GiroPetrenko/10g4psw/screenshots/1.jpg

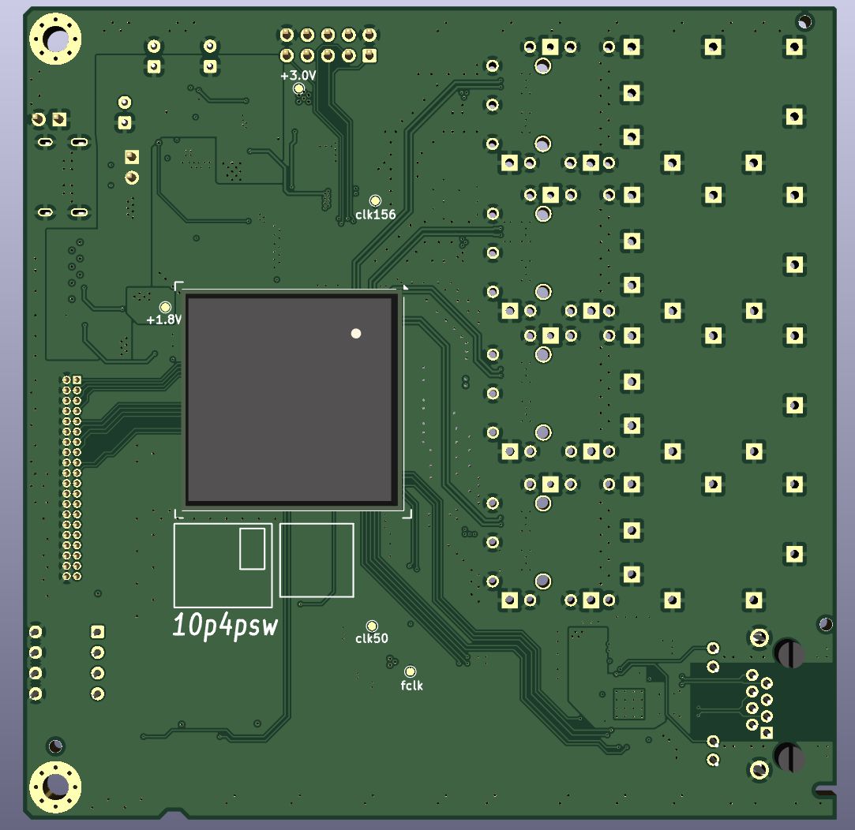
screenshots/1.jpg
