GiroPetrenko/10g4psw/10p_4psw.kicad_sch

## KiCad design 10p_4psw.kicad_sch (2025-11-05)

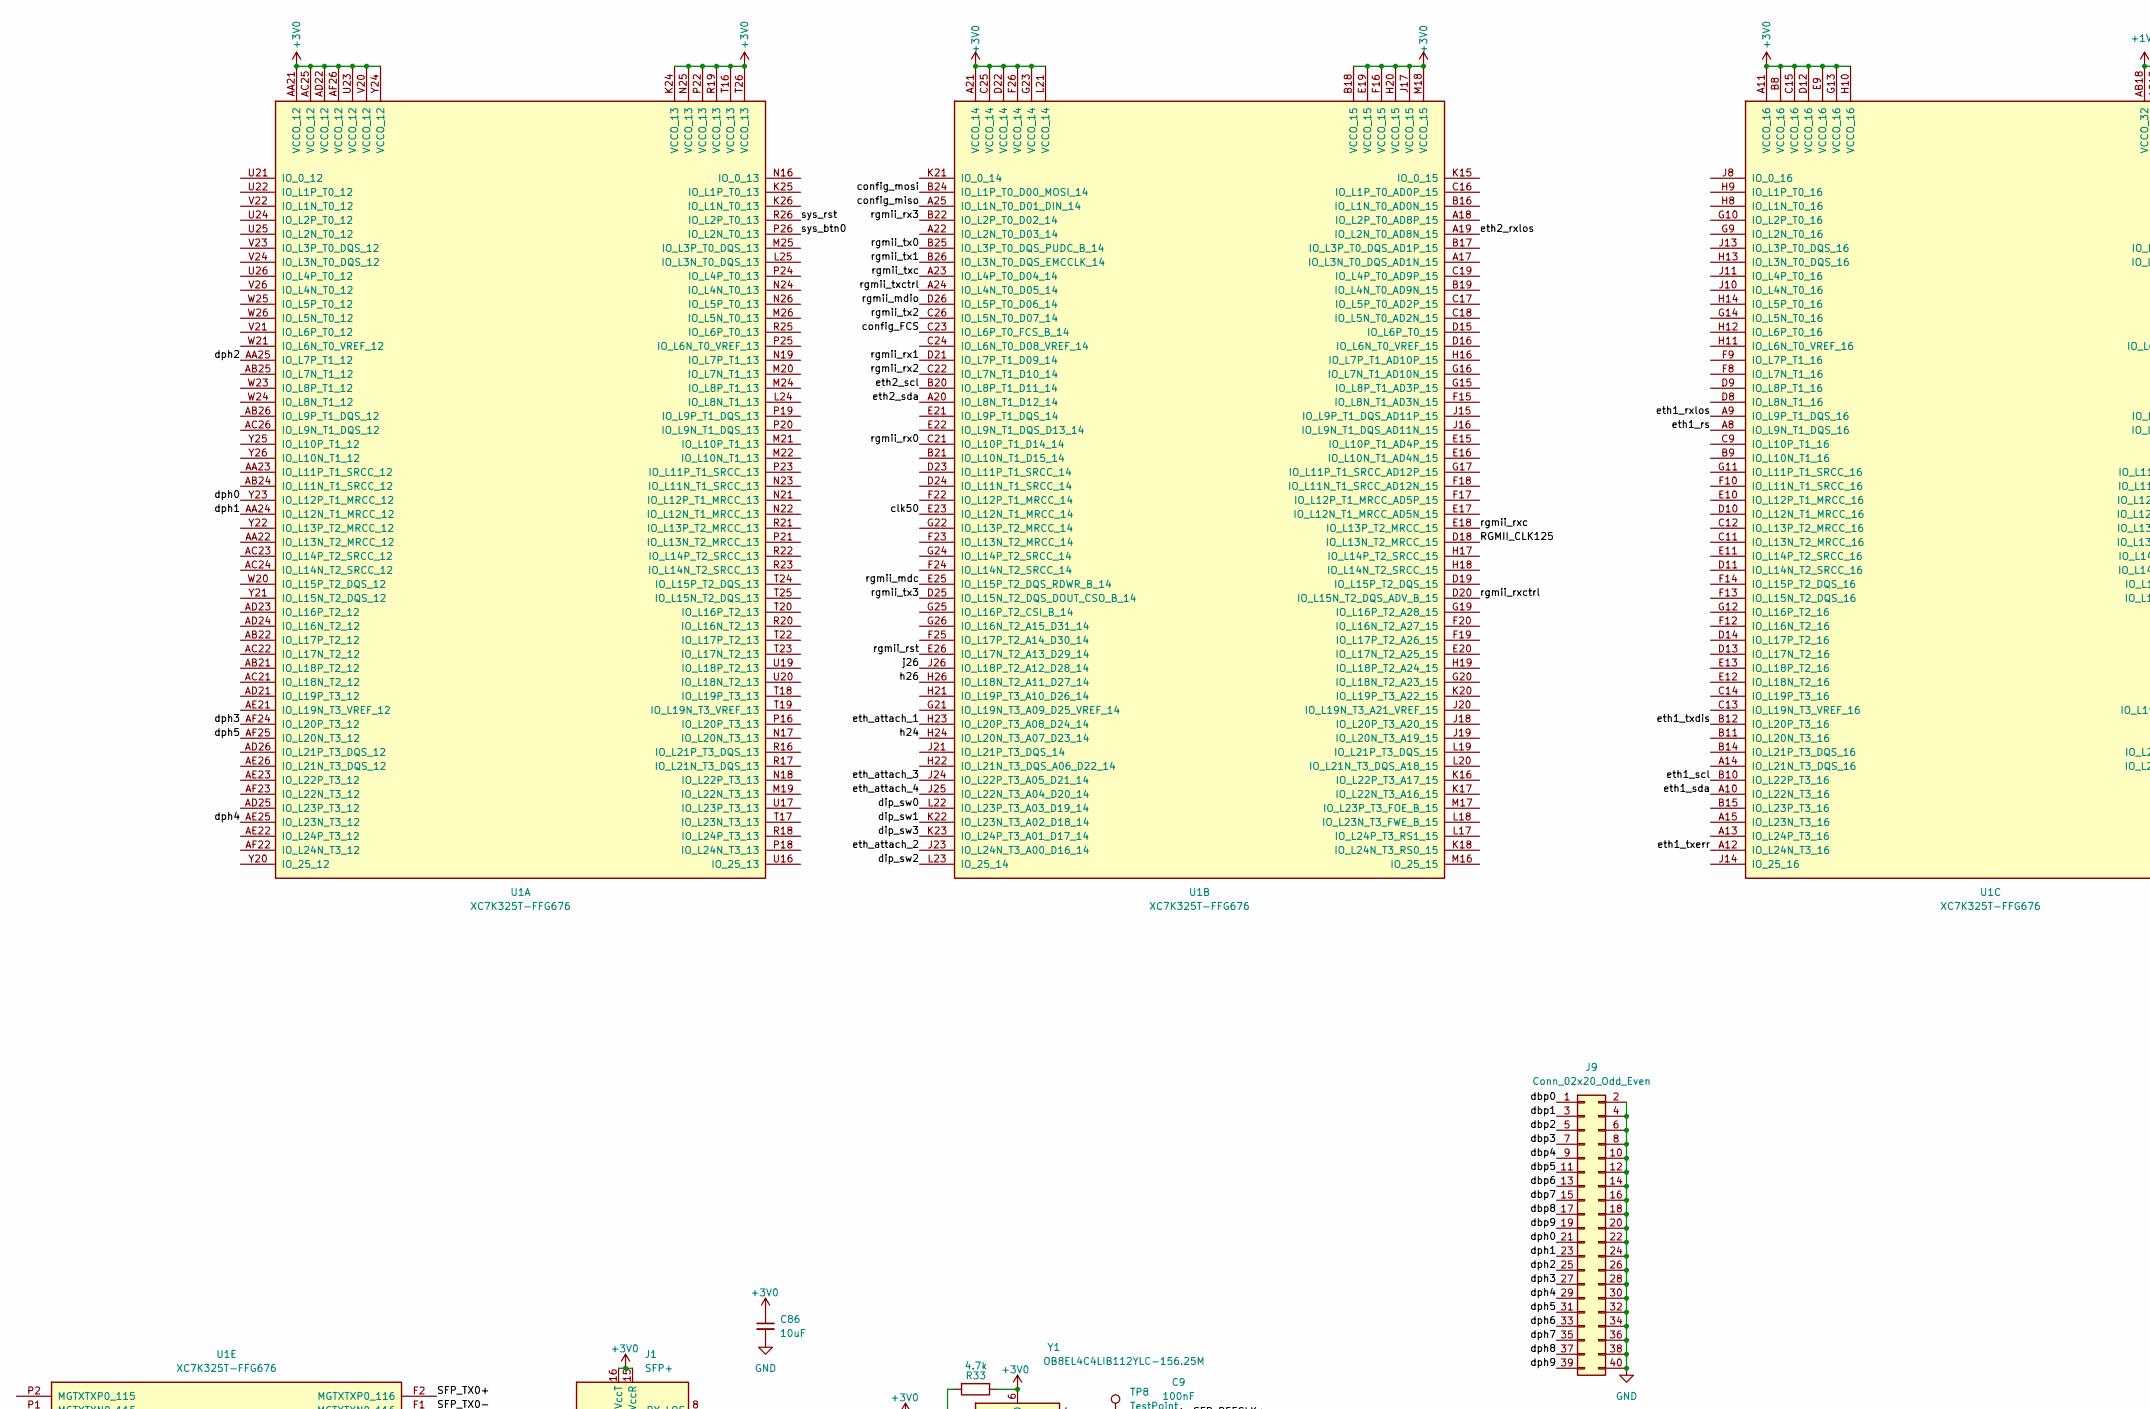
[picture p5: schematic 10p_4psw.kicad_sch, part in row 1, column 1]

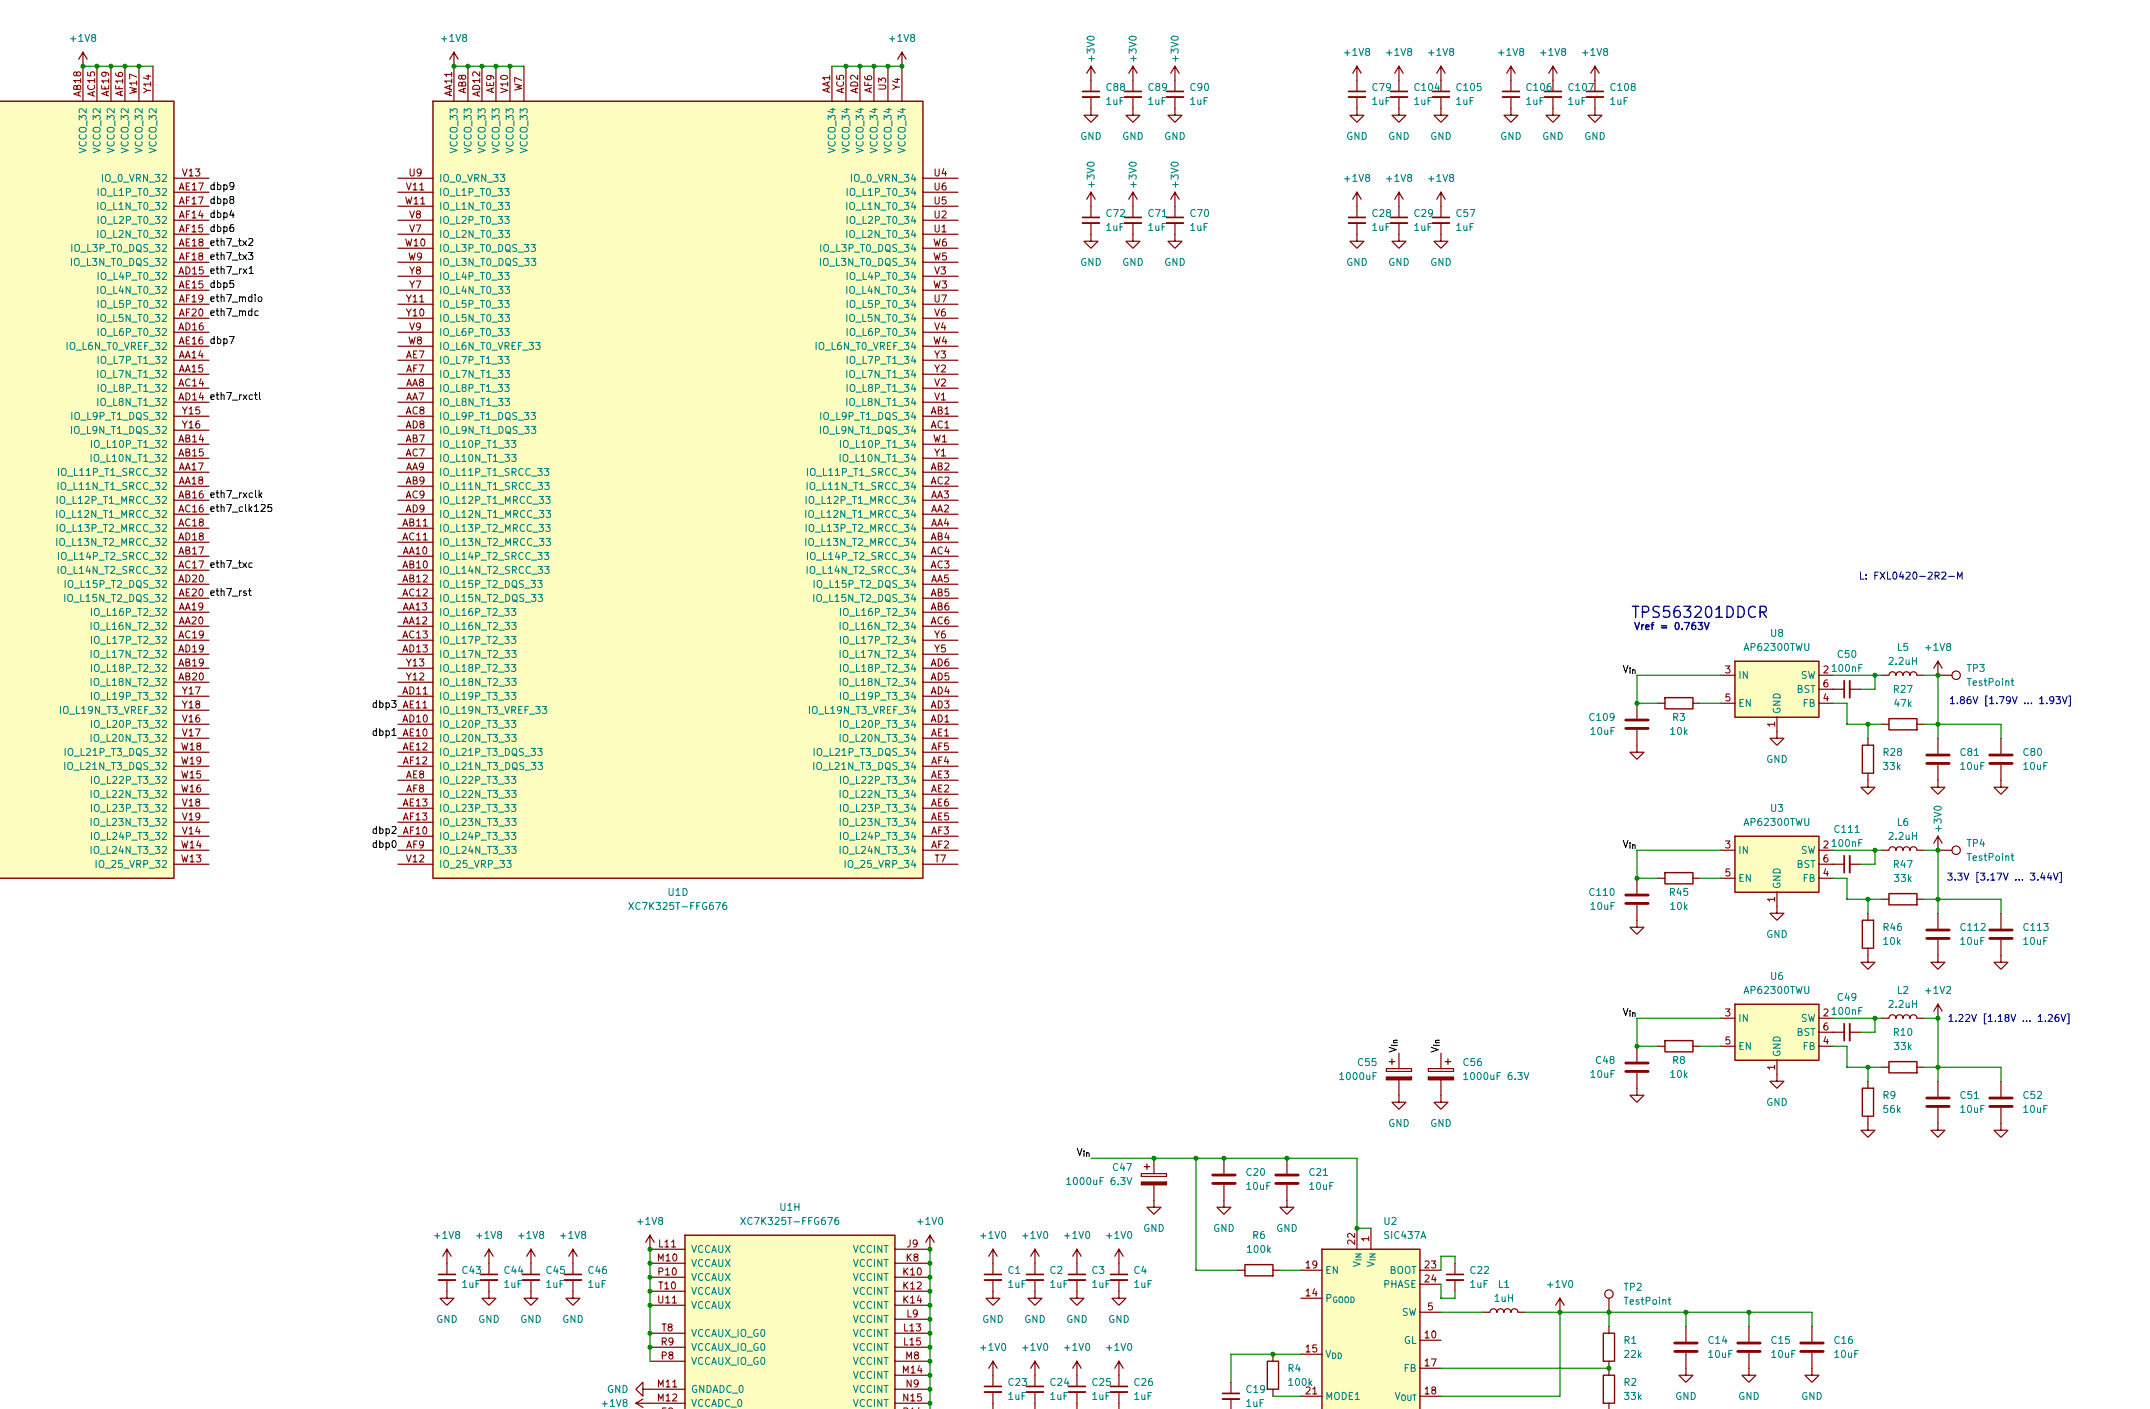
[picture p6: schematic 10p_4psw.kicad_sch, part in row 1, column 2]

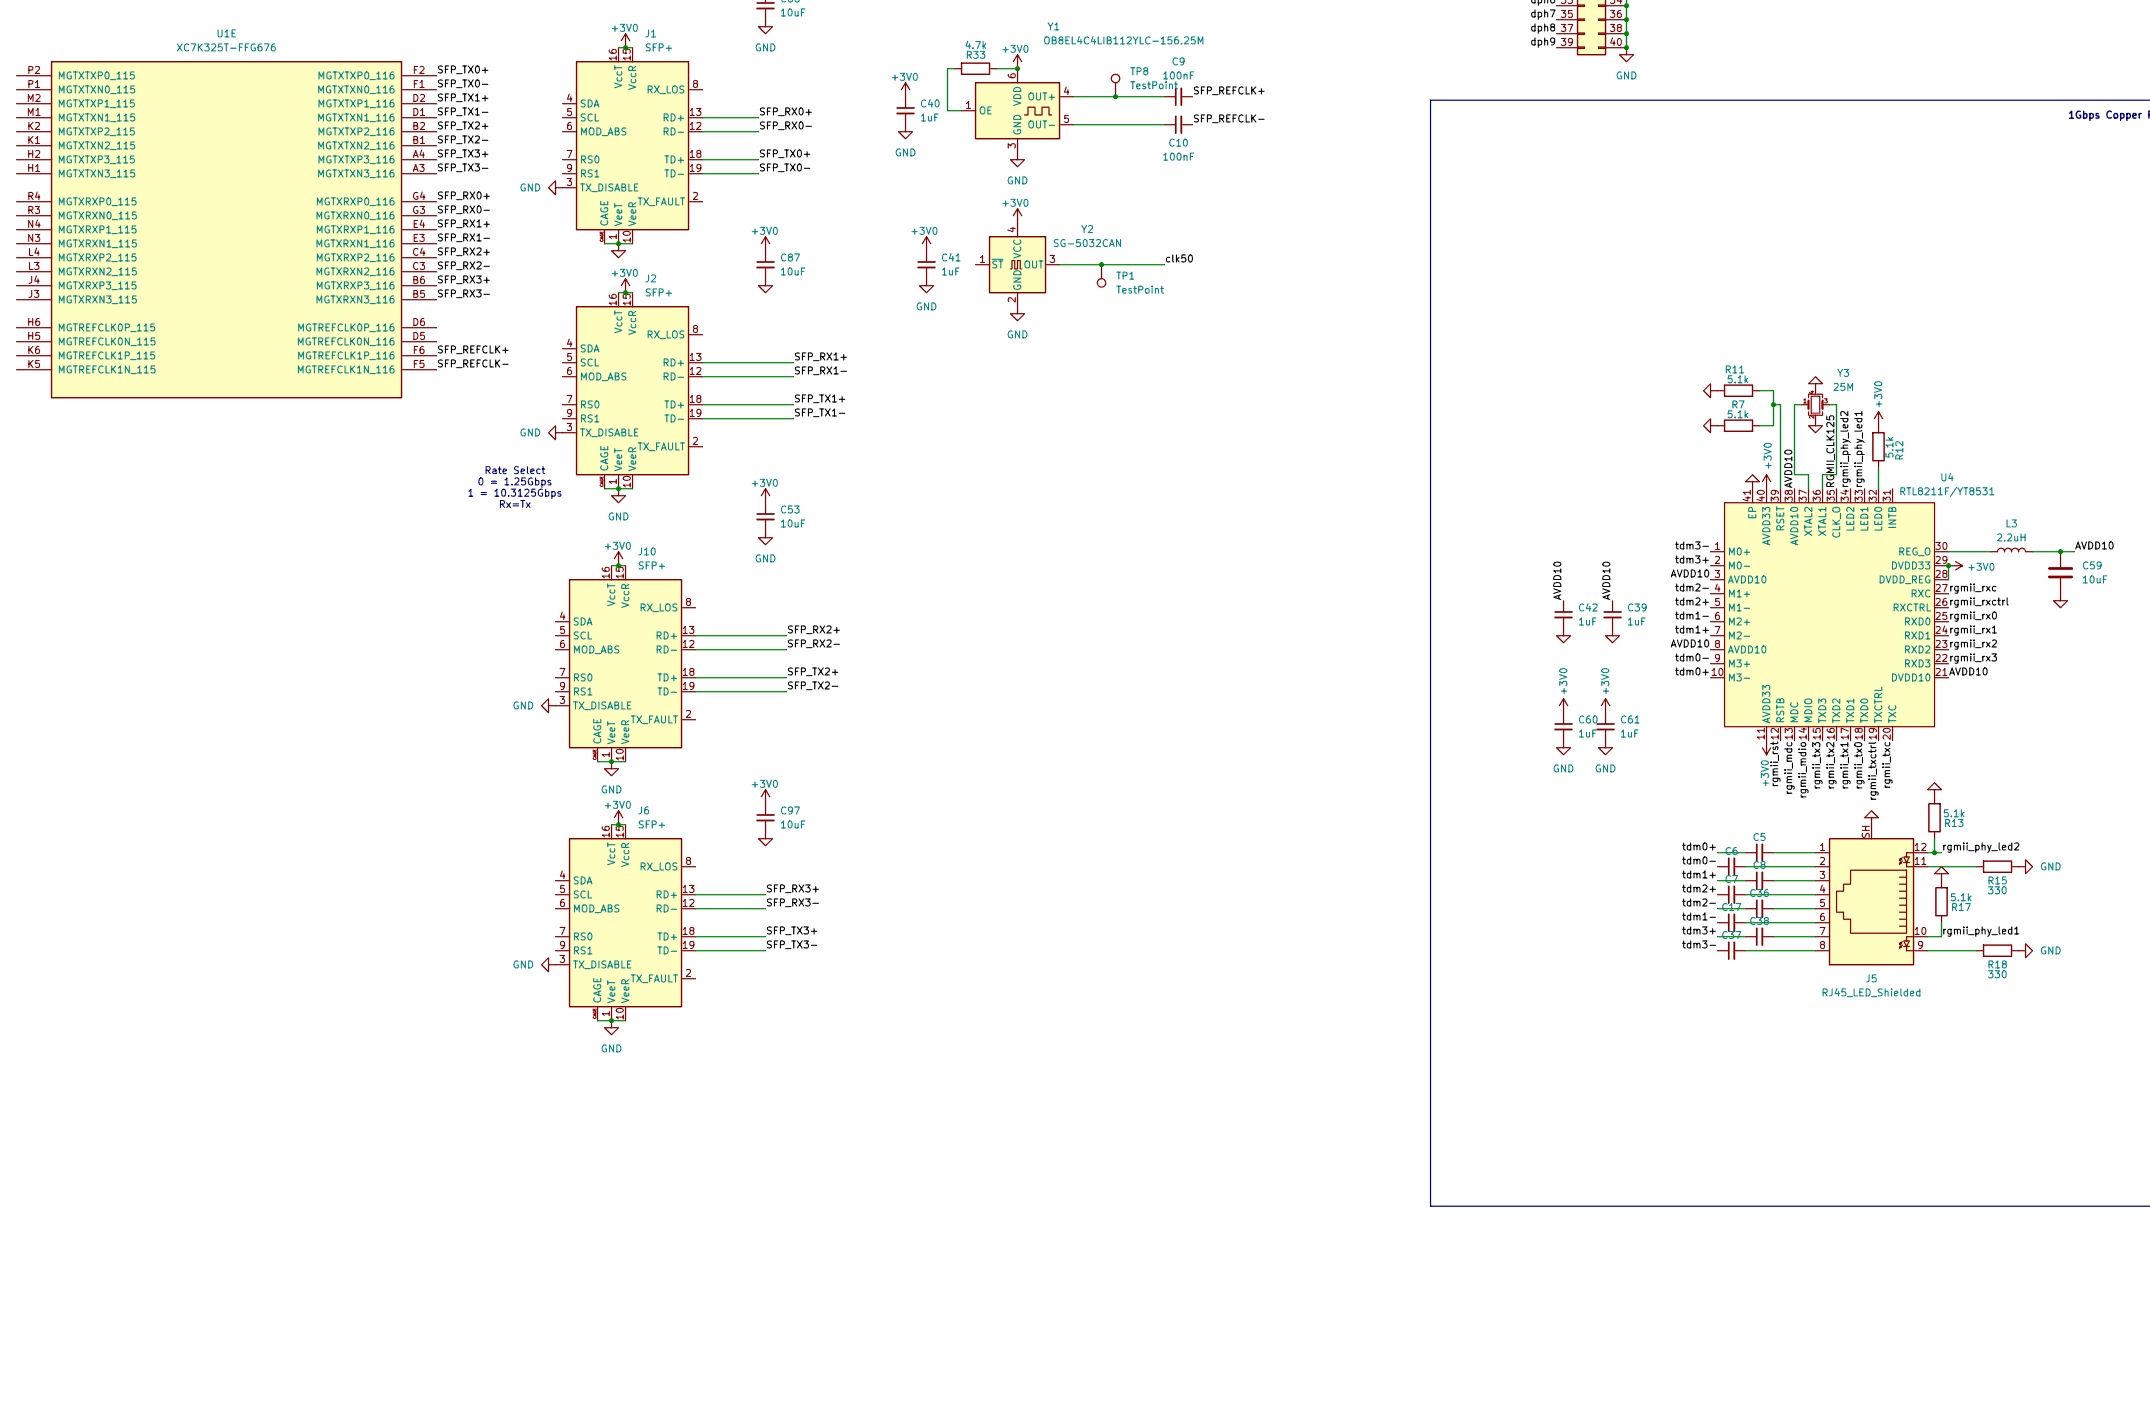
[picture p7: schematic 10p_4psw.kicad_sch, part in row 2, column 1]

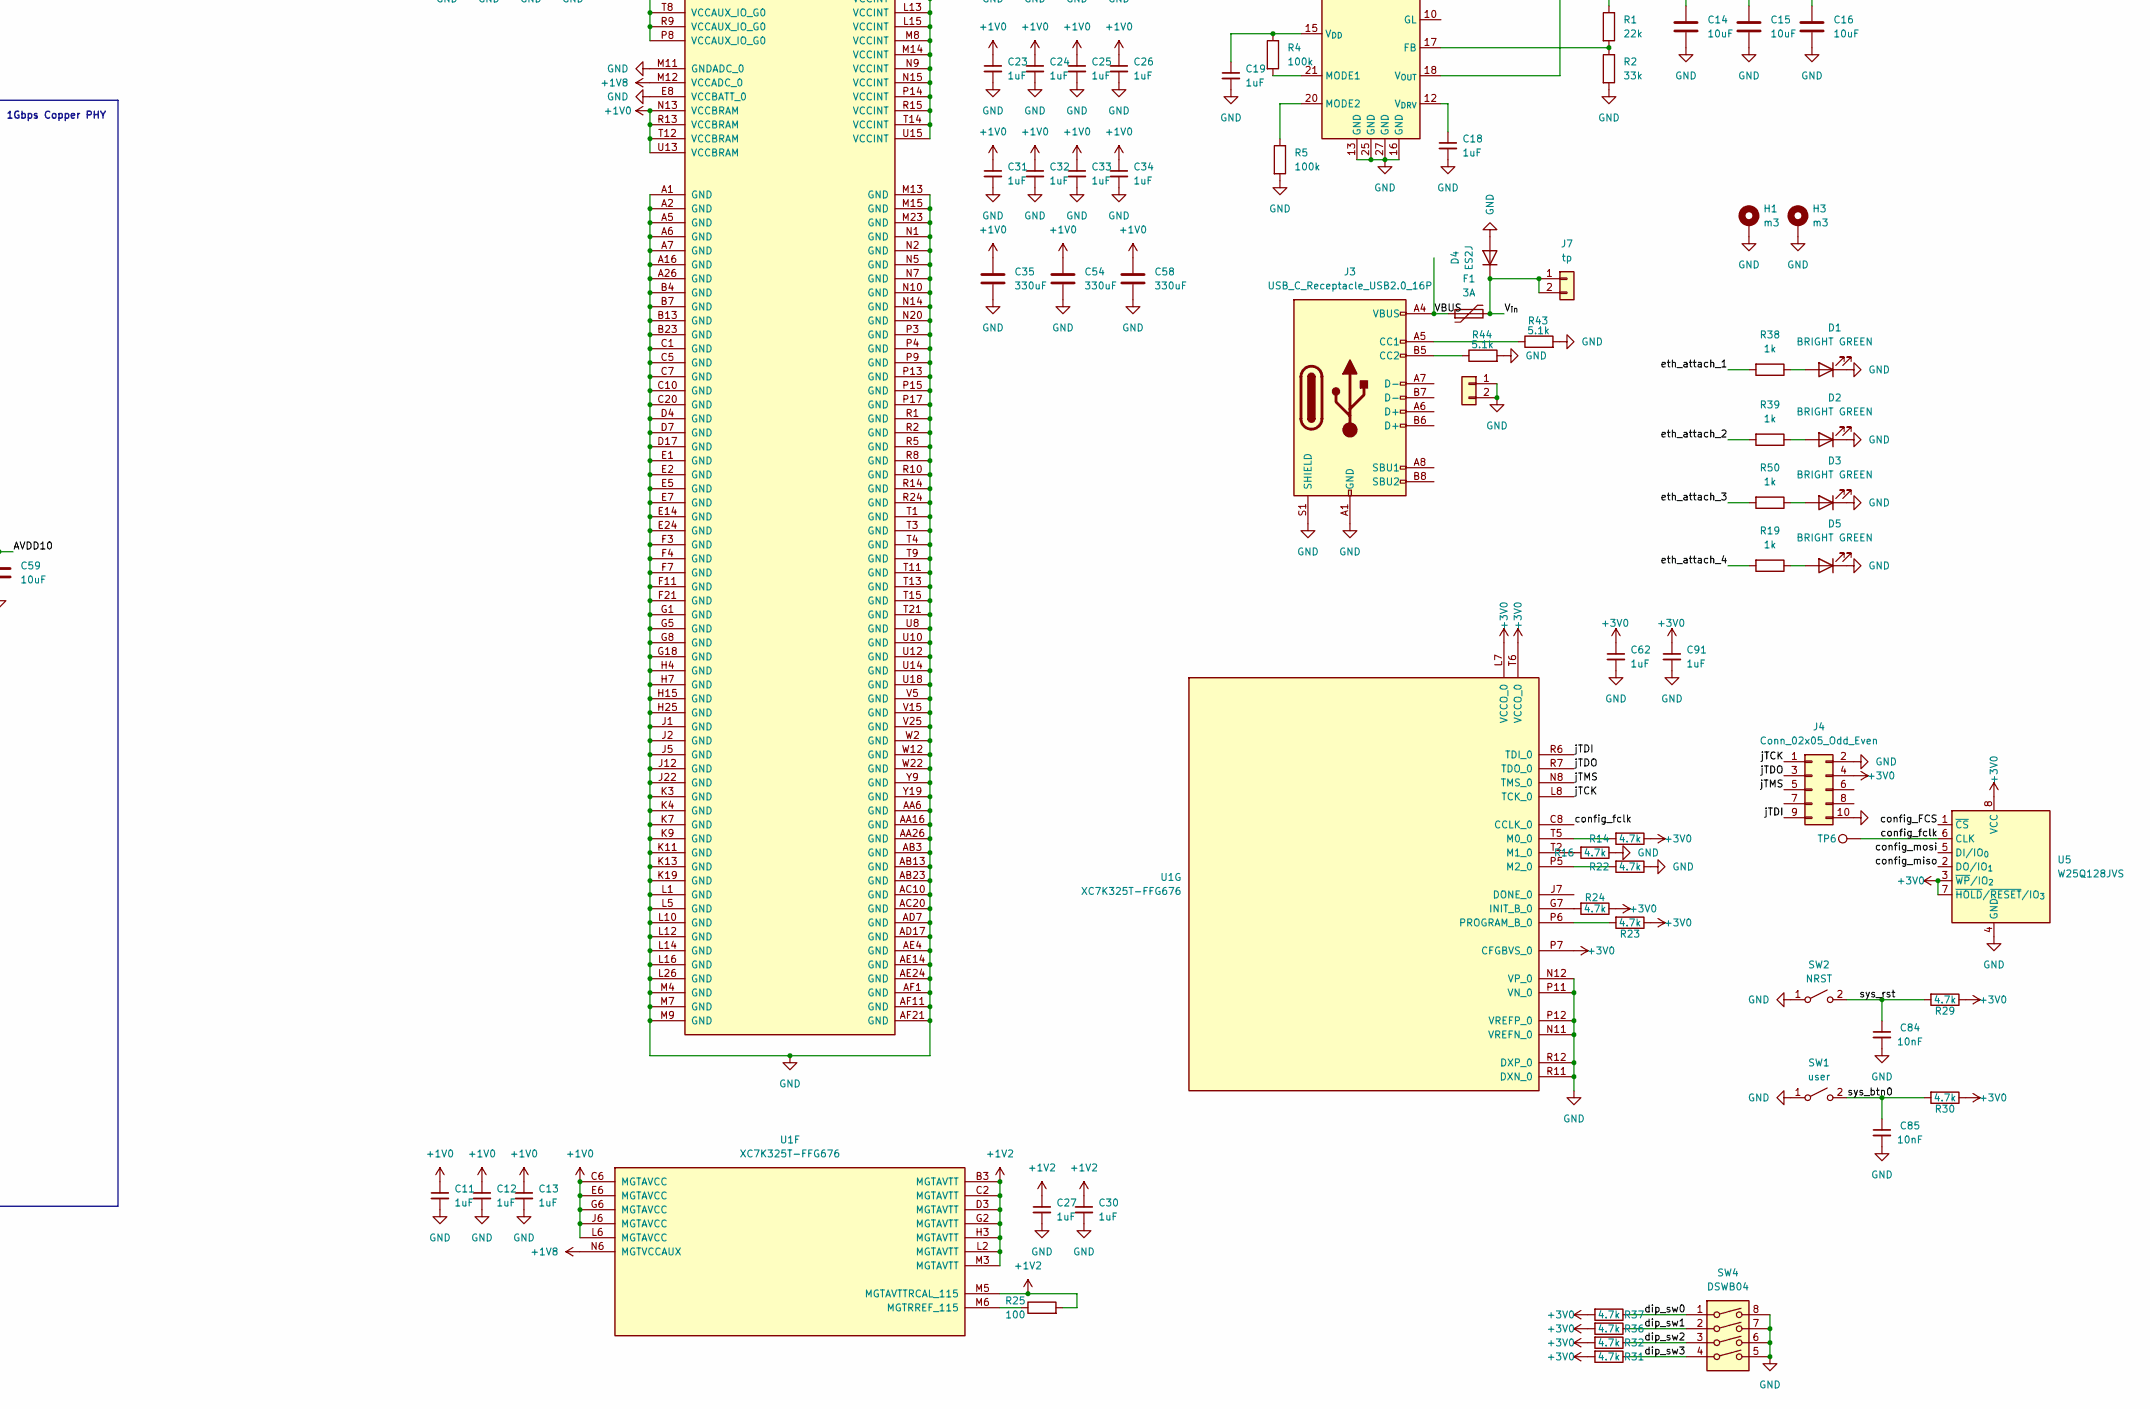
[picture p8: schematic 10p_4psw.kicad_sch, part in row 2, column 2]

Parts:
C1, C2, C3, C4, C5, C6, C7, C8, C11, C12, C13, C17, C18, C19, C22, C23, C24, C25, C26, C27, C28, C29, C30, C31, C32, C33, C34, C36, C37, C38, C39, C40, C41, C42, C43, C44, C45, C46, C57, C60, C61, C62, C70, C71, C72, C79, C88, C89, C90, C91, C104, C105, C106, C107, C108: 1uF; C_0402_1005Metric
C9, C10, C49, C50, C111: 100nF; C_0402_1005Metric
C14, C15, C16, C20, C21, C48, C51, C52, C53, C59, C80, C81, C86, C87, C97, C109, C110, C112, C113: 10uF; C_0805_2012Metric
C35, C54, C58: 330uF; C_1210_3225Metric
C47, C56: 1000uF 6.3V; CP_Radial_D6.3mm_P2.50mm
C55: 1000uF; CP_Radial_D6.3mm_P2.50mm
C84, C85: 10nF; C_0402_1005Metric
D1, D2, D3, D5: BRIGHT GREEN; LED_0805_2012Metric
D4: ES2J; D_SMB
F1: 3A; R_1812_4532Metric
H1, H3: m3; MountingHole_3.2mm_M3_Pad_Via
J1, J2, J6, J10: SFP+; Connector_SFP_and_Cage
J3: USB_C_Receptacle_USB2.0_16P; USB_C_12pin_usb2only_pwr
J4: Conn_02x05_Odd_Even; IDC-Header_2x05_P2.54mm_Vertical
J5: RJ45_LED_Shielded; RJ45_Amphenol_RJHSE538X
J7, J8: tp; PinHeader_1x02_P2.54mm_Vertical
J9: Conn_02x20_Odd_Even; PinHeader_2x20_P1.27mm_Vertical
L1: 1uH; L_1010_largePAD
L2, L3, L5, L6: 2.2uH; L_Sunlord_MWSA0412S
R1: 22k; R_0603_1608Metric
R2, R10, R28, R47: 33k; R_0603_1608Metric
R3, R8, R45: 10k; R_0402_1005Metric
R4, R5, R6: 100k; R_0603_1608Metric
R7, R11, R12, R13, R17, R43, R44: 5.1k; R_0402_1005Metric
R9: 56k; R_0603_1608Metric
R14, R16, R22, R23, R24, R29, R30, R31, R32, R33, R36, R37: 4.7k; R_0402_1005Metric
R15, R18: 330; R_0402_1005Metric
R19, R38, R39, R50: 1k; R_0603_1608Metric
R25: 100; R_0402_1005Metric
R27: 47k; R_0603_1608Metric
R46: 10k; R_0603_1608Metric
SW1: user; PTS645_btn3225_compat
SW2: NRST; PTS645_btn3225_compat
SW4: DSWB04; SW_DIP_SPSTx04_Slide_9.78x12.34mm_W7.62mm_P2.54mm
TP1, TP2, TP3, TP4, TP6, TP8: TestPoint; TestPoint_Pad_D1.0mm
U1: XC7K325T-FFG676; Xilinx_FFG676
U2: SIC437A; SiC43x_PowerPAK_MLP44
U3, U6, U8: AP62300TWU; TSOT-23-6
U4: RTL8211F/YT8531; QFN-40-1EP_5x5mm_P0.4mm_EP3.6x3.6mm_ThermalVias
U5: W25Q128JVS; SOIC-8_5.3x5.3mm_P1.27mm
Y1: OB8EL4C4LIB112YLC-156.25M; Oscillator_SMD_IDT_JS6-6_5.0x3.2mm_P1.27mm
Y2: SG-5032CAN; Oscillator_SMD_EuroQuartz_XO53-4Pin_5.0x3.2mm
Y3: 25M; Crystal_SMD_3225-4Pin_3.2x2.5mm

Connections:
+1V0: C1.1, C2.1, C3.1, C4.1, C11.1, C12.1, C13.1, C14.1, C15.1, C16.1, C23.1, C24.1, C25.1, C26.1, C31.1, C32.1, C33.1, C34.1, C35.1, C54.1, C58.1, L1.2, R1.1, TP2.1, U1.C6 (MGTAVCC), U1.E6 (MGTAVCC), U1.G6 (MGTAVCC), U1.J6 (MGTAVCC), U1.J9 (VCCINT), U1.K8 (VCCINT), U1.K10 (VCCINT), U1.K12 (VCCINT), U1.K14 (VCCINT), U1.L6 (MGTAVCC), U1.L9 (VCCINT), U1.L13 (VCCINT), U1.L15 (VCCINT), U1.M8 (VCCINT), U1.M14 (VCCINT), U1.N9 (VCCINT), U1.N13 (VCCBRAM), U1.N15 (VCCINT), U1.P14 (VCCINT), U1.R13 (VCCBRAM), U1.R15 (VCCINT), U1.T12 (VCCBRAM), U1.T14 (VCCINT), U1.U13 (VCCBRAM), U1.U15 (VCCINT), U2.18 (V_{OUT})
+1V2: C27.1, C30.1, C51.1, C52.1, L2.2, R10.2, R25.2, U1.B3 (MGTAVTT), U1.C2 (MGTAVTT), U1.D3 (MGTAVTT), U1.G2 (MGTAVTT), U1.H3 (MGTAVTT), U1.L2 (MGTAVTT), U1.M3 (MGTAVTT), U1.M5 (MGTAVTTRCAL_115)
+1V8: C28.1, C29.1, C43.1, C44.1, C45.1, C46.1, C57.1, C79.1, C80.1, C81.1, C104.1, C105.1, C106.1, C107.1, C108.1, L5.2, R27.2, TP3.1, U1.AA1 (VCCO_34), U1.AA11 (VCCO_33), U1.AB8 (VCCO_33), U1.AB18 (VCCO_32), U1.AC5 (VCCO_34), U1.AC15 (VCCO_32), U1.AD2 (VCCO_34), U1.AD12 (VCCO_33), U1.AE9 (VCCO_33), U1.AE19 (VCCO_32), U1.AF6 (VCCO_34), U1.AF16 (VCCO_32), U1.L11 (VCCAUX), U1.M10 (VCCAUX), U1.M12 (VCCADC_0), U1.N6 (MGTVCCAUX), U1.P8 (VCCAUX_IO_G0), U1.P10 (VCCAUX), U1.R9 (VCCAUX_IO_G0), U1.T8 (VCCAUX_IO_G0), U1.T10 (VCCAUX), U1.U3 (VCCO_34), U1.U11 (VCCAUX), U1.V10 (VCCO_33), U1.W7 (VCCO_33), U1.W17 (VCCO_32), U1.Y4 (VCCO_34), U1.Y14 (VCCO_32)
+3V0: C40.1, C41.1, C53.1, C60.1, C61.1, C62.1, C70.1, C71.1, C72.1, C86.1, C87.1, C88.1, C89.1, C90.1, C91.1, C97.1, C112.1, C113.1, J1.15 (VccR), J1.16 (VccT), J2.15 (VccR), J2.16 (VccT), J4.4, J6.15 (VccR), J6.16 (VccT), J10.15 (VccR), J10.16 (VccT), L6.2, R12.2, R14.1, R23.1, R24.1, R29.1, R30.1, R31.2, R32.2, R33.1, R36.2, R37.2, R47.2, TP4.1, U1.A11 (VCCO_16), U1.A21 (VCCO_14), U1.AA21 (VCCO_12), U1.AC25 (VCCO_12), U1.AD22 (VCCO_12), U1.AF26 (VCCO_12), U1.B8 (VCCO_16), U1.B18 (VCCO_15), U1.C15 (VCCO_16), U1.C25 (VCCO_14), U1.D12 (VCCO_16), U1.D22 (VCCO_14), U1.E9 (VCCO_16), U1.E19 (VCCO_15), U1.F16 (VCCO_15), U1.F26 (VCCO_14), U1.G13 (VCCO_16), U1.G23 (VCCO_14), U1.H10 (VCCO_16), U1.H20 (VCCO_15), U1.J17 (VCCO_15), U1.K24 (VCCO_13), U1.L7 (VCCO_0), U1.L21 (VCCO_14), U1.M18 (VCCO_15), U1.N25 (VCCO_13), U1.P7 (CFGBVS_0), U1.P22 (VCCO_13), U1.R19 (VCCO_13), U1.T6 (VCCO_0), U1.T16 (VCCO_13), U1.T26 (VCCO_13), U1.U23 (VCCO_12), U1.V20 (VCCO_12), U1.Y24 (VCCO_12), U4.11 (AVDD33), U4.28 (DVDD_REG), U4.29 (DVDD33), U4.40 (AVDD33), U5.3 (~WP/IO_{2}), U5.7 (~HOLD/~RESET/IO_{3}), U5.8 (VCC), Y1.6 (VDD), Y2.4 (VCC)
AVDD10: C39.1, C42.1, C59.1, L3.2, U4.3 (AVDD10), U4.8 (AVDD10), U4.21 (DVDD10), U4.38 (AVDD10)
GND: C1.2, C2.2, C3.2, C4.2, C11.2, C12.2, C13.2, C14.2, C15.2, C16.2, C18.2, C19.2, C20.2, C21.2, C23.2, C24.2, C25.2, C26.2, C27.2, C28.2, C29.2, C30.2, C31.2, C32.2, C33.2, C34.2, C35.2, C39.2, C40.2, C41.2, C42.2, C43.2, C44.2, C45.2, C46.2, C47.2, C48.2, C51.2, C52.2, C53.2, C54.2, C55.2, C56.2, C57.2, C58.2, C59.2, C60.2, C61.2, C62.2, C70.2, C71.2, C72.2, C79.2, C80.2, C81.2, C84.2, C85.2, C86.2, C87.2, C88.2, C89.2, C90.2, C91.2, C97.2, C104.2, C105.2, C106.2, C107.2, C108.2, C109.2, C110.2, C112.2, C113.2, D1.1 (K), D2.1 (K), D3.1 (K), D4.2 (A), D5.1 (K), H1.1, H3.1, J1.1 (VeeT), J1.3 (TX_DISABLE), J1.10 (VeeR), J1.11 (VeeR), J1.14 (VeeR), J1.17 (VeeT), J1.20 (VeeT), J1.CAGE, J2.1 (VeeT), J2.3 (TX_DISABLE), J2.10 (VeeR), J2.11 (VeeR), J2.14 (VeeR), J2.17 (VeeT), J2.20 (VeeT), J2.CAGE, J3.A1 (GND), J3.A12 (GND), J3.B1 (GND), J3.B12 (GND), J3.S1 (SHIELD), J4.2, J4.10, J5.SH, J6.1 (VeeT), J6.3 (TX_DISABLE), J6.10 (VeeR), J6.11 (VeeR), J6.14 (VeeR), J6.17 (VeeT), J6.20 (VeeT), J6.CAGE, J8.1, J8.2, J9.2, J9.4, J9.6, J9.8, J9.10, J9.12, J9.14, J9.16, J9.18, J9.20, J9.22, J9.24, J9.26, J9.28, J9.30, J9.32, J9.34, J9.36, J9.38, J9.40, J10.1 (VeeT), J10.3 (TX_DISABLE), J10.10 (VeeR), J10.11 (VeeR), J10.14 (VeeR), J10.17 (VeeT), J10.20 (VeeT), J10.CAGE, R2.2, R5.2, R7.1, R9.1, R11.1, R13.2, R15.1, R16.1, R17.2, R18.1, R22.1, R28.1, R43.2, R44.2, R46.1, SW1.1 (A), SW2.1 (A), SW4.5, SW4.6, SW4.7, SW4.8, U1.A1 (GND), U1.A2 (GND), U1.A5 (GND), U1.A6 (GND), U1.A7 (GND), U1.A16 (GND), U1.A26 (GND), U1.AA6 (GND), U1.AA16 (GND), U1.AA26 (GND), U1.AB3 (GND), U1.AB13 (GND), U1.AB23 (GND), U1.AC10 (GND), U1.AC20 (GND), U1.AD7 (GND), U1.AD17 (GND), U1.AE4 (GND), U1.AE14 (GND), U1.AE24 (GND), U1.AF1 (GND), U1.AF11 (GND), U1.AF21 (GND), U1.B4 (GND), U1.B7 (GND), U1.B13 (GND), U1.B23 (GND), U1.C1 (GND), U1.C5 (GND), U1.C7 (GND), U1.C10 (GND), U1.C20 (GND), U1.D4 (GND), U1.D7 (GND), U1.D17 (GND), U1.E1 (GND), U1.E2 (GND), U1.E5 (GND), U1.E7 (GND), U1.E8 (VCCBATT_0), U1.E14 (GND), U1.E24 (GND), U1.F3 (GND), U1.F4 (GND), U1.F7 (GND), U1.F11 (GND), U1.F21 (GND), U1.G1 (GND), U1.G5 (GND), U1.G8 (GND), U1.G18 (GND), U1.H4 (GND), U1.H7 (GND), U1.H15 (GND), U1.H25 (GND), U1.J1 (GND), U1.J2 (GND), U1.J5 (GND), U1.J12 (GND), U1.J22 (GND), U1.K3 (GND), U1.K4 (GND), U1.K7 (GND), U1.K9 (GND), U1.K11 (GND), U1.K13 (GND), U1.K19 (GND), U1.L1 (GND), U1.L5 (GND), U1.L10 (GND), U1.L12 (GND), U1.L14 (GND), U1.L16 (GND), U1.L26 (GND), U1.M4 (GND), U1.M7 (GND), U1.M9 (GND), U1.M11 (GNDADC_0), U1.M13 (GND), U1.M15 (GND), U1.M23 (GND), U1.N1 (GND), U1.N2 (GND), U1.N5 (GND), U1.N7 (GND), U1.N10 (GND), U1.N11 (VREFN_0), U1.N12 (VP_0), U1.N14 (GND), U1.N20 (GND), U1.P3 (GND), U1.P4 (GND), U1.P9 (GND), U1.P11 (VN_0), U1.P12 (VREFP_0), U1.P13 (GND), U1.P15 (GND), U1.P17 (GND), U1.R1 (GND), U1.R2 (GND), U1.R5 (GND), U1.R8 (GND), U1.R10 (GND), U1.R11 (DXN_0), U1.R12 (DXP_0), U1.R14 (GND), U1.R24 (GND), U1.T1 (GND), U1.T3 (GND), U1.T4 (GND), U1.T9 (GND), U1.T11 (GND), U1.T13 (GND), U1.T15 (GND), U1.T21 (GND), U1.U8 (GND), U1.U10 (GND), U1.U12 (GND), U1.U14 (GND), U1.U18 (GND), U1.V5 (GND), U1.V15 (GND), U1.V25 (GND), U1.W2 (GND), U1.W12 (GND), U1.W22 (GND), U1.Y9 (GND), U1.Y19 (GND), U2.13 (GND), U2.16 (GND), U2.25 (GND), U2.27 (GND), U3.1 (GND), U4.41 (EP), U5.4 (GND), U6.1 (GND), U8.1 (GND), Y1.3 (GND), Y2.2 (GND), Y3.2, Y3.4
unnamed: C5.2, J5.1
unnamed: C6.2, J5.2
unnamed: C7.2, J5.4
unnamed: C8.2, J5.3
unnamed: C9.1, TP8.1, Y1.4 (OUT+)
unnamed: C10.1, Y1.5 (OUT-)
unnamed: C17.2, J5.6
unnamed: C18.1, U2.12 (V_{DRV})
unnamed: C19.1, R4.1, U2.15 (V_{DD})
unnamed: C22.1, U2.23 (BOOT)
unnamed: C22.2, U2.24 (PHASE)
unnamed: C36.2, J5.5
unnamed: C37.2, J5.8
unnamed: C38.2, J5.7
unnamed: C49.1, U6.6 (BST)
unnamed: C49.2, L2.1, U6.2 (SW)
unnamed: C50.1, U8.6 (BST)
unnamed: C50.2, L5.1, U8.2 (SW)
unnamed: C111.1, U3.6 (BST)
unnamed: C111.2, L6.1, U3.2 (SW)
unnamed: D1.2 (A), R38.1
unnamed: D2.2 (A), R39.1
unnamed: D3.2 (A), R50.1
unnamed: D5.2 (A), R19.1
unnamed: J3.A5 (CC1), R43.1
unnamed: J3.B5 (CC2), R44.1
unnamed: J5.9, R18.2
unnamed: J5.11, R15.2
unnamed: L1.1, U2.5 (SW)
unnamed: L3.1, U4.30 (REG_O)
unnamed: R1.2, R2.1, U2.17 (FB)
unnamed: R3.1, U8.5 (EN)
unnamed: R4.2, U2.21 (MODE1)
unnamed: R5.1, U2.20 (MODE2)
unnamed: R6.2, U2.19 (EN)
unnamed: R8.1, U6.5 (EN)
unnamed: R9.2, R10.1, U6.4 (FB)
unnamed: R7.2, R11.2, U4.39 (RSET)
unnamed: R12.1, U4.32 (LED0)
unnamed: R14.2, U1.T5 (M0_0)
unnamed: R16.2, U1.T2 (M1_0)
unnamed: R22.2, U1.P5 (M2_0)
unnamed: R23.2, U1.P6 (PROGRAM_B_0)
unnamed: R24.2, U1.G7 (INIT_B_0)
unnamed: R25.1, U1.M6 (MGTRREF_115)
unnamed: R27.1, R28.2, U8.4 (FB)
unnamed: R33.2, Y1.1 (OE)
unnamed: R45.1, U3.5 (EN)
unnamed: R46.2, R47.1, U3.4 (FB)
unnamed: U2.10 (GL), U2.11 (GL), U2.28 (GL)
unnamed: U4.36 (XTAL1), Y3.3
unnamed: U4.37 (XTAL2), Y3.1
RGMII_CLK125: U1.D18 (IO_L13N_T2_MRCC_15), U4.35 (CLK_O)
SFP_REFCLK+: C9.2, U1.F6 (MGTREFCLK1P_116)
SFP_REFCLK-: C10.2, U1.F5 (MGTREFCLK1N_116)
SFP_RX0+: J1.13 (RD+), U1.G4 (MGTXRXP0_116)
SFP_RX0-: J1.12 (RD-), U1.G3 (MGTXRXN0_116)
SFP_RX1+: J2.13 (RD+), U1.E4 (MGTXRXP1_116)
SFP_RX1-: J2.12 (RD-), U1.E3 (MGTXRXN1_116)
SFP_RX2+: J10.13 (RD+), U1.C4 (MGTXRXP2_116)
SFP_RX2-: J10.12 (RD-), U1.C3 (MGTXRXN2_116)
SFP_RX3+: J6.13 (RD+), U1.B6 (MGTXRXP3_116)
SFP_RX3-: J6.12 (RD-), U1.B5 (MGTXRXN3_116)
SFP_TX0+: J1.18 (TD+), U1.F2 (MGTXTXP0_116)
SFP_TX0-: J1.19 (TD-), U1.F1 (MGTXTXN0_116)
SFP_TX1+: J2.18 (TD+), U1.D2 (MGTXTXP1_116)
SFP_TX1-: J2.19 (TD-), U1.D1 (MGTXTXN1_116)
SFP_TX2+: J10.18 (TD+), U1.B2 (MGTXTXP2_116)
SFP_TX2-: J10.19 (TD-), U1.B1 (MGTXTXN2_116)
SFP_TX3+: J6.18 (TD+), U1.A4 (MGTXTXP3_116)
SFP_TX3-: J6.19 (TD-), U1.A3 (MGTXTXN3_116)
VBUS: F1.1, J3.A4 (VBUS), J3.A9 (VBUS), J3.B4 (VBUS), J3.B9 (VBUS)
V_{in}: C20.1, C21.1, C47.1, C48.1, C55.1, C56.1, C109.1, C110.1, D4.1 (K), F1.2, J7.1, J7.2, R3.2, R6.1, R8.2, R45.2, U2.1 (V_{IN}), U2.22 (V_{IN}), U3.3 (IN), U6.3 (IN), U8.3 (IN)
clk50: TP1.1, U1.E23 (IO_L12N_T1_MRCC_14), Y2.3 (OUT)
config_FCS: U1.C23 (IO_L6P_T0_FCS_B_14), U5.1 (~CS)
config_fclk: TP6.1, U1.C8 (CCLK_0), U5.6 (CLK)
config_miso: U1.A25 (IO_L1N_T0_D01_DIN_14), U5.2 (DO/IO_{1})
config_mosi: U1.B24 (IO_L1P_T0_D00_MOSI_14), U5.5 (DI/IO_{0})
dbp0: J9.1, U1.AF9 (IO_L24N_T3_33)
dbp1: J9.3, U1.AE10 (IO_L20N_T3_33)
dbp2: J9.5, U1.AF10 (IO_L24P_T3_33)
dbp3: J9.7, U1.AE11 (IO_L19N_T3_VREF_33)
dbp4: J9.9, U1.AF14 (IO_L2P_T0_32)
dbp5: J9.11, U1.AE15 (IO_L4N_T0_32)
dbp6: J9.13, U1.AF15 (IO_L2N_T0_32)
dbp7: J9.15, U1.AE16 (IO_L6N_T0_VREF_32)
dbp8: J9.17, U1.AF17 (IO_L1N_T0_32)
dbp9: J9.19, U1.AE17 (IO_L1P_T0_32)
dip_sw0: R37.1, SW4.1, U1.L22 (IO_L23P_T3_A03_D19_14)
dip_sw1: R36.1, SW4.2, U1.K22 (IO_L23N_T3_A02_D18_14)
dip_sw2: R32.1, SW4.3, U1.L23 (IO_25_14)
dip_sw3: R31.1, SW4.4, U1.K23 (IO_L24P_T3_A01_D17_14)
dph0: J9.21, U1.Y23 (IO_L12P_T1_MRCC_12)
dph1: J9.23, U1.AA24 (IO_L12N_T1_MRCC_12)
dph2: J9.25, U1.AA25 (IO_L7P_T1_12)
dph3: J9.27, U1.AF24 (IO_L20P_T3_12)
dph4: J9.29, U1.AE25 (IO_L23N_T3_12)
dph5: J9.31, U1.AF25 (IO_L20N_T3_12)
dph6: J9.33
dph7: J9.35
dph8: J9.37
dph9: J9.39
eth1_rs: U1.A8 (IO_L9N_T1_DQS_16)
eth1_rxlos: U1.A9 (IO_L9P_T1_DQS_16)
eth1_scl: U1.B10 (IO_L22P_T3_16)
eth1_sda: U1.A10 (IO_L22N_T3_16)
eth1_txdis: U1.B12 (IO_L20P_T3_16)
eth1_txerr: U1.A12 (IO_L24N_T3_16)
eth2_rxlos: U1.A19 (IO_L2N_T0_AD8N_15)
eth2_scl: U1.B20 (IO_L8P_T1_D11_14)
eth2_sda: U1.A20 (IO_L8N_T1_D12_14)
eth7_clk125: U1.AC16 (IO_L12N_T1_MRCC_32)
eth7_mdc: U1.AF20 (IO_L5N_T0_32)
eth7_mdio: U1.AF19 (IO_L5P_T0_32)
eth7_rst: U1.AE20 (IO_L15N_T2_DQS_32)
eth7_rx1: U1.AD15 (IO_L4P_T0_32)
eth7_rxclk: U1.AB16 (IO_L12P_T1_MRCC_32)
eth7_rxctl: U1.AD14 (IO_L8N_T1_32)
eth7_tx2: U1.AE18 (IO_L3P_T0_DQS_32)
eth7_tx3: U1.AF18 (IO_L3N_T0_DQS_32)
eth7_txc: U1.AC17 (IO_L14N_T2_SRCC_32)
eth_attach_1: R38.2, U1.H23 (IO_L20P_T3_A08_D24_14)
eth_attach_2: R39.2, U1.J23 (IO_L24N_T3_A00_D16_14)
eth_attach_3: R50.2, U1.J24 (IO_L22P_T3_A05_D21_14)
eth_attach_4: R19.2, U1.J25 (IO_L22N_T3_A04_D20_14)
h24: U1.H24 (IO_L20N_T3_A07_D23_14)
h26: U1.H26 (IO_L18N_T2_A11_D27_14)
j26: U1.J26 (IO_L18P_T2_A12_D28_14)
jTCK: J4.1, U1.L8 (TCK_0)
jTDI: J4.9, U1.R6 (TDI_0)
jTDO: J4.3, U1.R7 (TDO_0)
jTMS: J4.5, U1.N8 (TMS_0)
rgmii_mdc: U1.E25 (IO_L15P_T2_DQS_RDWR_B_14), U4.13 (MDC)
rgmii_mdio: U1.D26 (IO_L5P_T0_D06_14), U4.14 (MDIO)
rgmii_phy_led1: J5.10, R17.1, U4.33 (LED1)
rgmii_phy_led2: J5.12, R13.1, U4.34 (LED2)
rgmii_rst: U1.E26 (IO_L17N_T2_A13_D29_14), U4.12 (RSTB)
rgmii_rx0: U1.C21 (IO_L10P_T1_D14_14), U4.25 (RXD0)
rgmii_rx1: U1.D21 (IO_L7P_T1_D09_14), U4.24 (RXD1)
rgmii_rx2: U1.C22 (IO_L7N_T1_D10_14), U4.23 (RXD2)
rgmii_rx3: U1.B22 (IO_L2P_T0_D02_14), U4.22 (RXD3)
rgmii_rxc: U1.E18 (IO_L13P_T2_MRCC_15), U4.27 (RXC)
rgmii_rxctrl: U1.D20 (IO_L15N_T2_DQS_ADV_B_15), U4.26 (RXCTRL)
rgmii_tx0: U1.B25 (IO_L3P_T0_DQS_PUDC_B_14), U4.18 (TXD0)
rgmii_tx1: U1.B26 (IO_L3N_T0_DQS_EMCCLK_14), U4.17 (TXD1)
rgmii_tx2: U1.C26 (IO_L5N_T0_D07_14), U4.16 (TXD2)
rgmii_tx3: U1.D25 (IO_L15N_T2_DQS_DOUT_CSO_B_14), U4.15 (TXD3)
rgmii_txc: U1.A23 (IO_L4P_T0_D04_14), U4.20 (TXC)
rgmii_txctrl: U1.A24 (IO_L4N_T0_D05_14), U4.19 (TXCTRL)
sys_btn0: C85.1, R30.2, SW1.2 (B), U1.P26 (IO_L2N_T0_13)
sys_rst: C84.1, R29.2, SW2.2 (B), U1.R26 (IO_L2P_T0_13)
tdm0+: C5.1, U4.10 (M3-)
tdm0-: C6.1, U4.9 (M3+)
tdm1+: C8.1, U4.7 (M2-)
tdm1-: C17.1, U4.6 (M2+)
tdm2+: C7.1, U4.5 (M1-)
tdm2-: C36.1, U4.4 (M1+)
tdm3+: C38.1, U4.2 (M0-)
tdm3-: C37.1, U4.1 (M0+)

Notes on the sheet:
TPS563201DDCR
1.86V [1.79V ... 1.93V]
1Gbps Copper PHY
3.3V [3.17V ... 3.44V]
L: FXL0420-2R2-M
Rate Select 0 = 1.25Gbps 1 = 10.3125Gbps Rx=Tx
1.22V [1.18V ... 1.26V]
Vref = 0.763V
